bigtreetech/Eddy/3D/EDDY_PRINT_PARTS/Eddy_TapV2/Eddy-Tap V2 (3).jpg

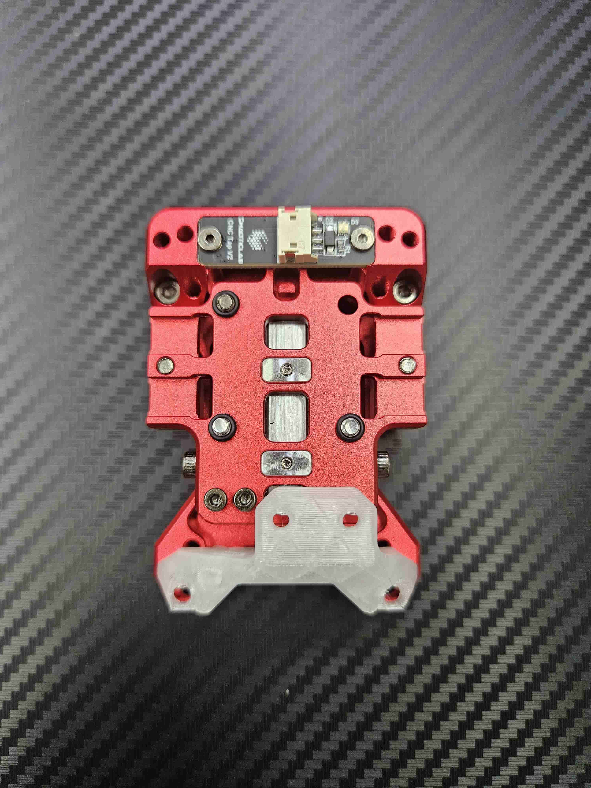
3D/EDDY_PRINT_PARTS/Eddy_TapV2/Eddy-Tap V2 (3).jpg
