bigtreetech/Eddy/3D/EDDY_PRINT_PARTS/Eddy_TapV2/Eddy-Tap V2 (4).jpg

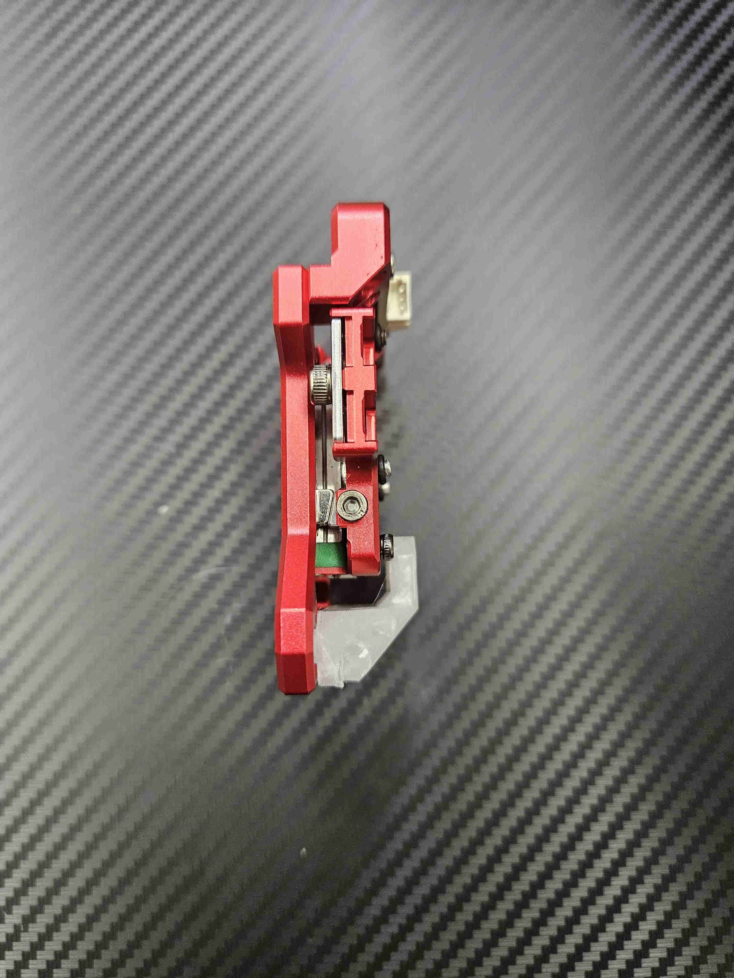
3D/EDDY_PRINT_PARTS/Eddy_TapV2/Eddy-Tap V2 (4).jpg
