bigtreetech/Eddy/Images/printercfg.png

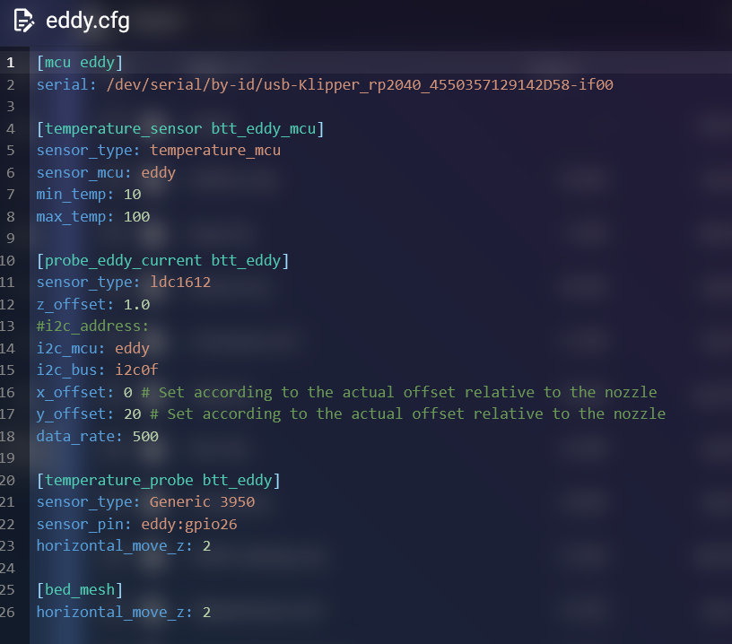
Images/printercfg.png
