bigtreetech/Eddy/3D/EDDY_PRINT_PARTS/Community_Mods/Eddy_Calibration_Block/Eddy-Mount-IMG_20240510_201000.jpg

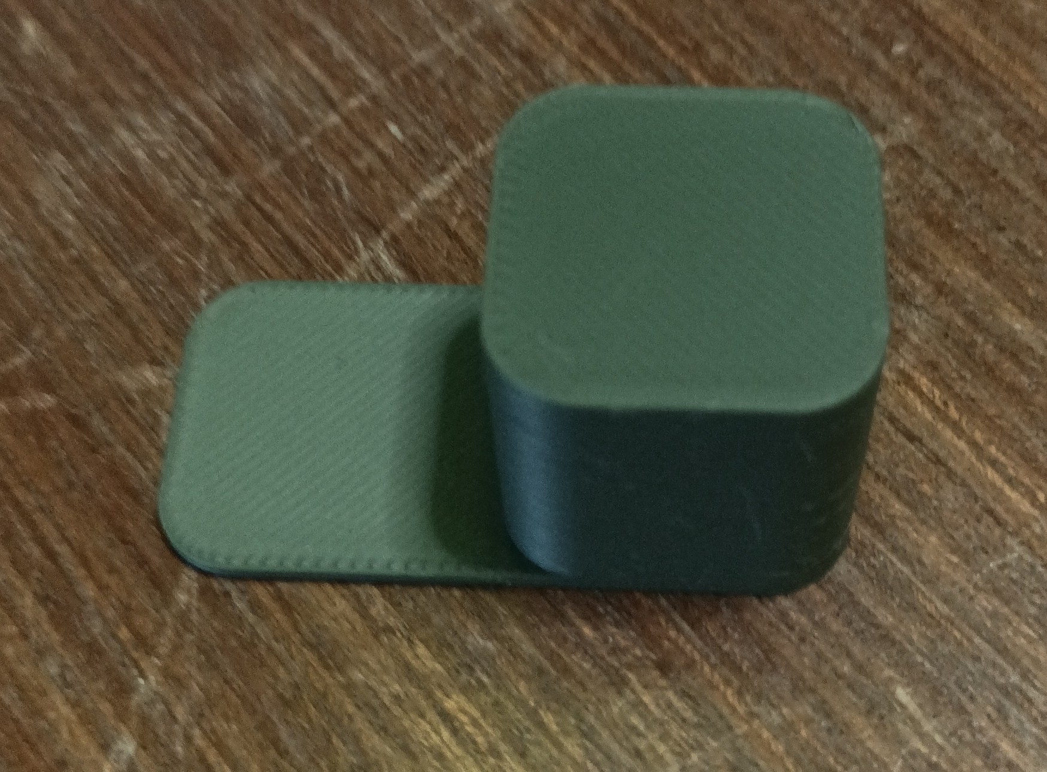
3D/EDDY_PRINT_PARTS/Community_Mods/Eddy_Calibration_Block/Eddy-Mount-IMG_20240510_201000.jpg
